tugsi/Filaman/html/set_spoolman.png

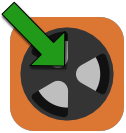
html/set_spoolman.png
