tugsi/Filaman/html/spool_in.png

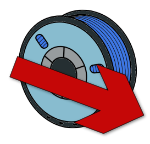
html/spool_in.png
