tugsi/Filaman/img/display_2.png

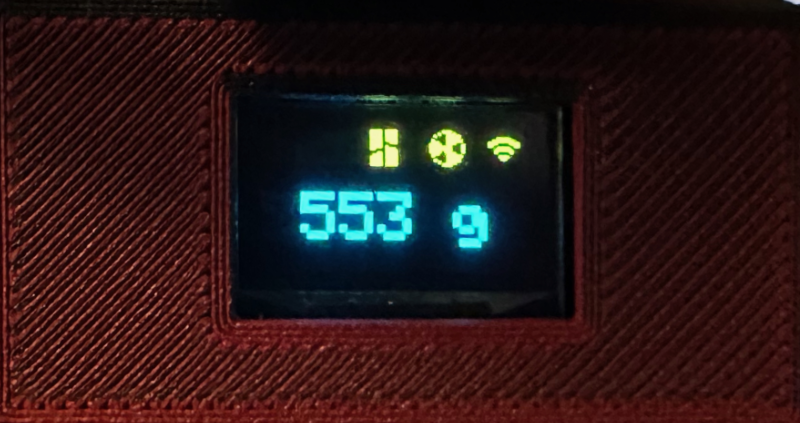
img/display_2.png
