tugsi/Filaman/img/display_3.png

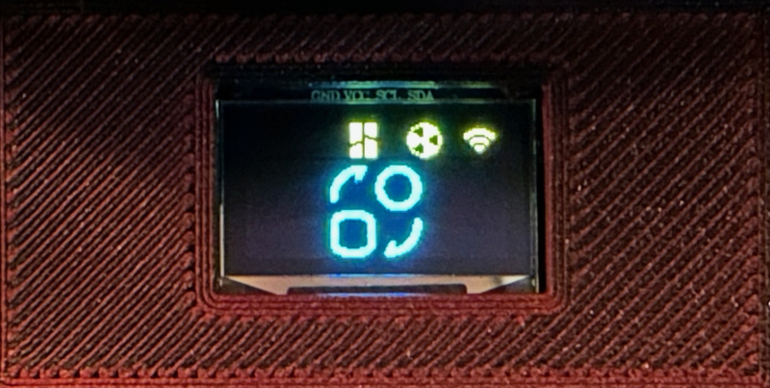
img/display_3.png
