tugsi/Filaman/img/ESP32-SPI-Pins.png

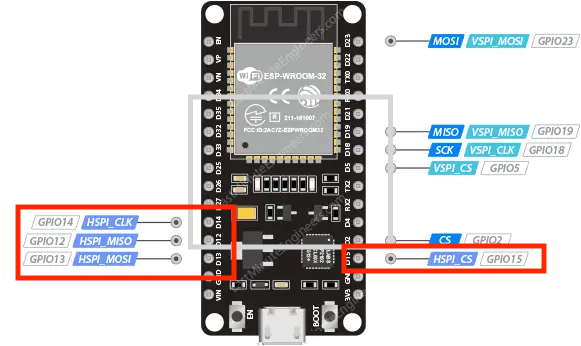
img/ESP32-SPI-Pins.png
