tugsi/Filaman/img/scale_2.png

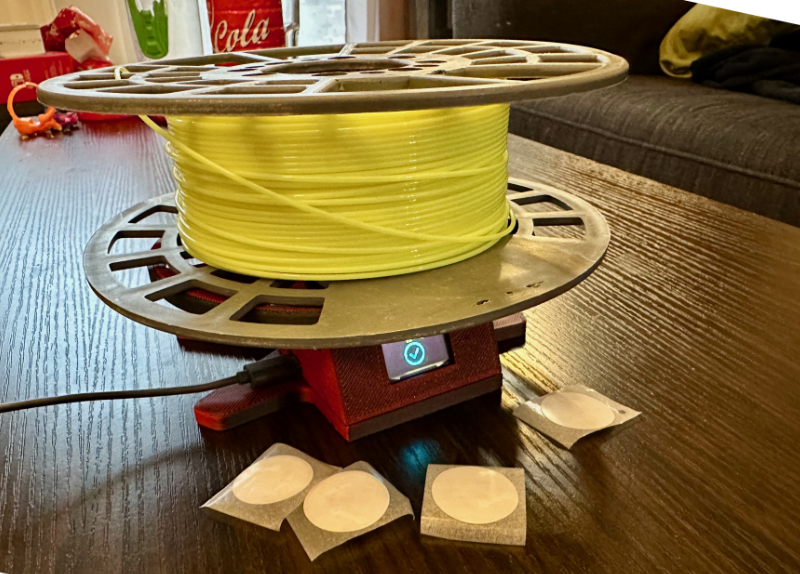
img/scale_2.png
