tugsi/Filaman/img/scale_3.png

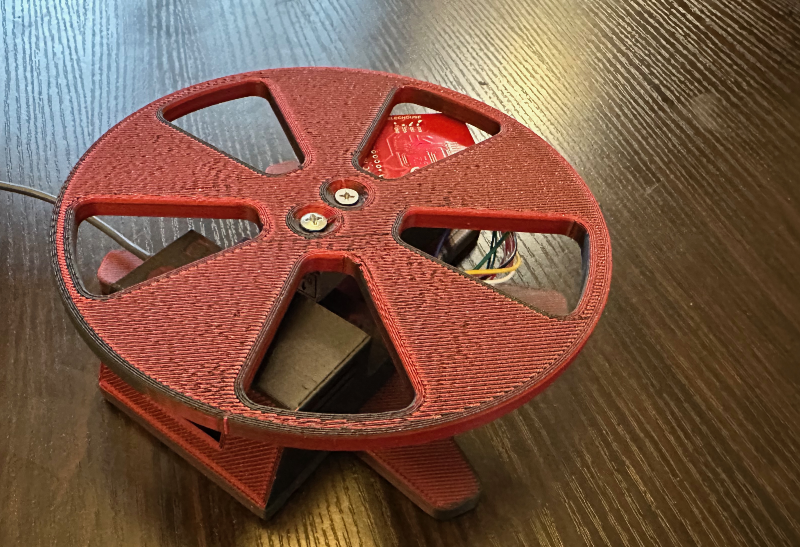
img/scale_3.png
