tugsi/Filaman/img/scale_4.png

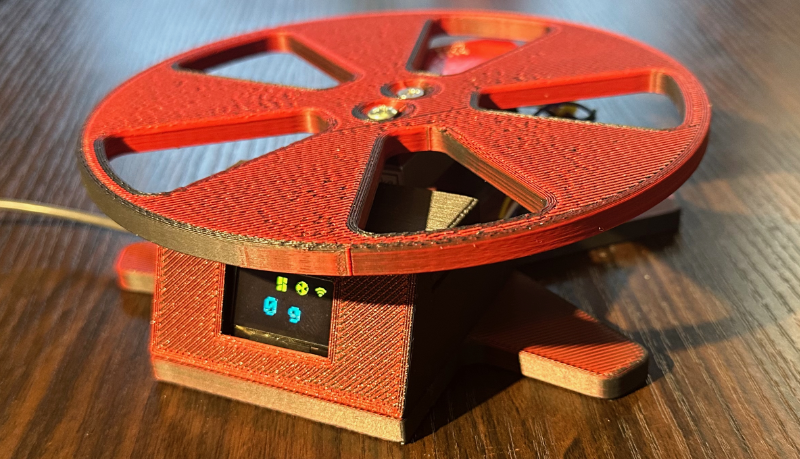
img/scale_4.png
