tugsi/Filaman/img/scale_side.png

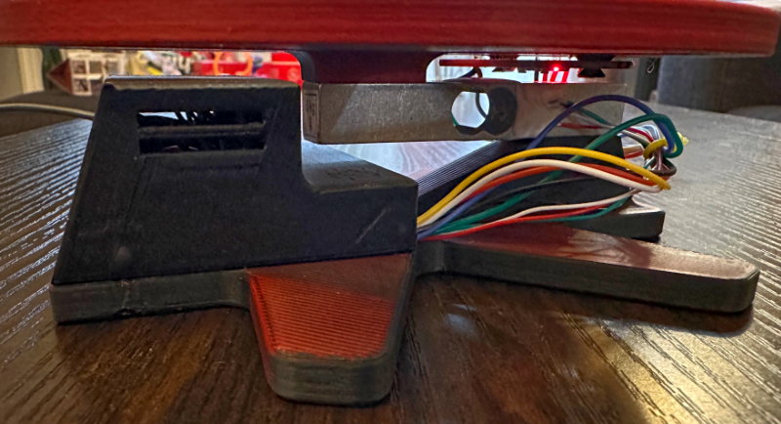
img/scale_side.png
