tugsi/Filaman/img/web_1.jpeg

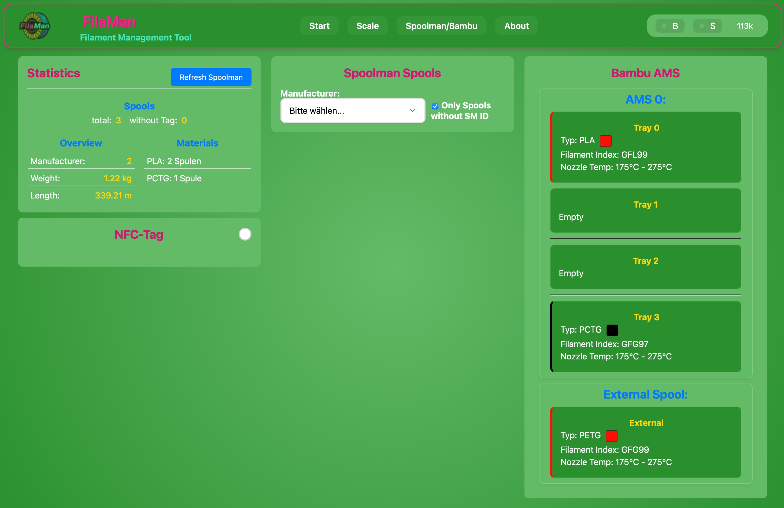
img/web_1.jpeg
