tugsi/Filaman/img/web_ams.png

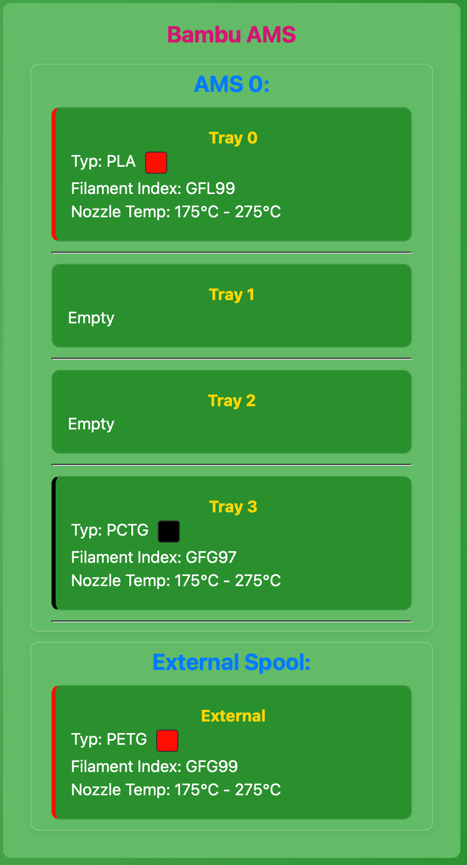
img/web_ams.png
