tugsi/Filaman/img/web_spoolm_to_ams.png

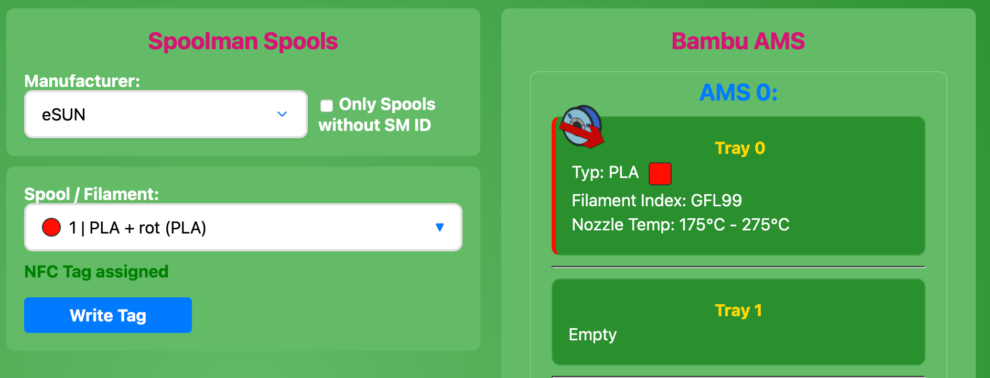
img/web_spoolm_to_ams.png
