tugsi/Filaman/img/web_statistics.png

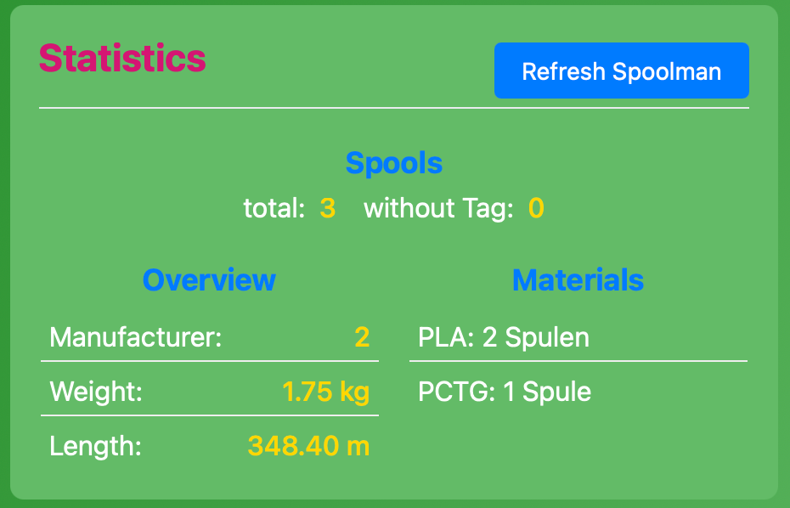
img/web_statistics.png
