tugsi/Filaman/usermod/spitzbirne32/Images/Display_measurement/Display1_usermod_spitzbirne32.jpg

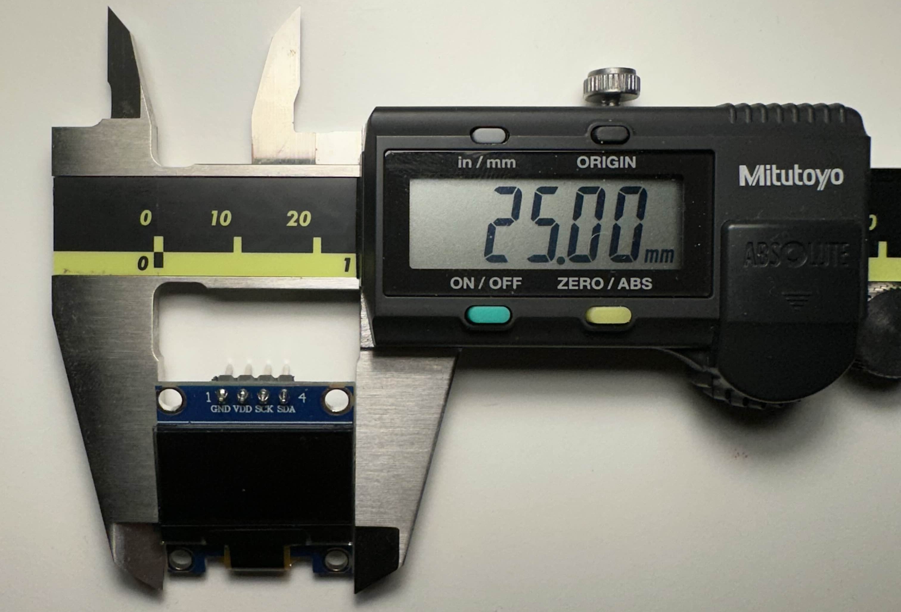
usermod/spitzbirne32/Images/Display_measurement/Display1_usermod_spitzbirne32.jpg
