tugsi/Filaman/usermod/spitzbirne32/Images/Scale_measurement/Scale_Holespacing_usermod_spitzbirne32.jpg

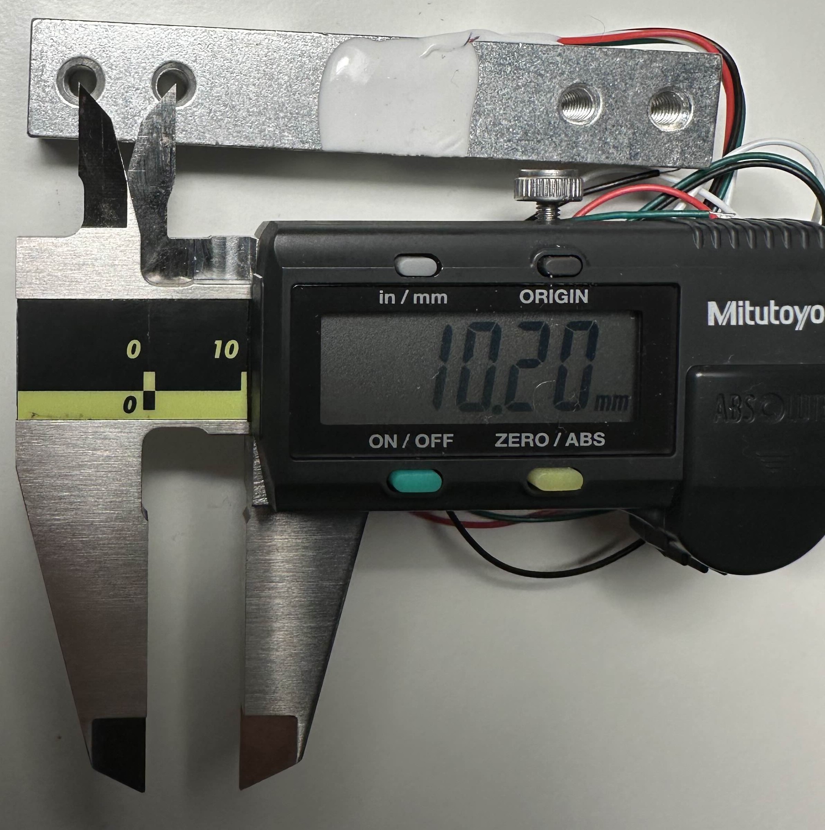
usermod/spitzbirne32/Images/Scale_measurement/Scale_Holespacing_usermod_spitzbirne32.jpg
